djvanderlaan/led-visualisation-rotterdam/punch_card_reader/card_text/signature.scad

cube([92, 35, 1]);

color("black")
linear_extrude(2)
import("test2.svg", convexity=100);
